Cryptoblade9623/zmk-config/Kicad Files/case left1.png

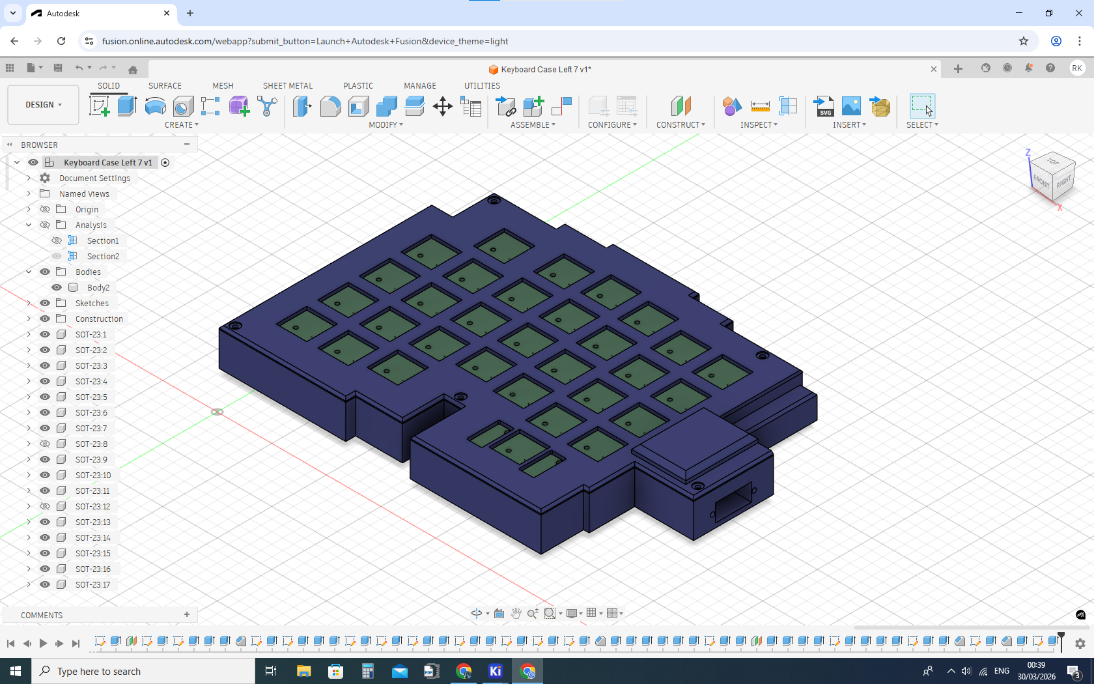
Kicad Files/case left1.png
