Cryptoblade9623/zmk-config/Kicad Files/case right1.png

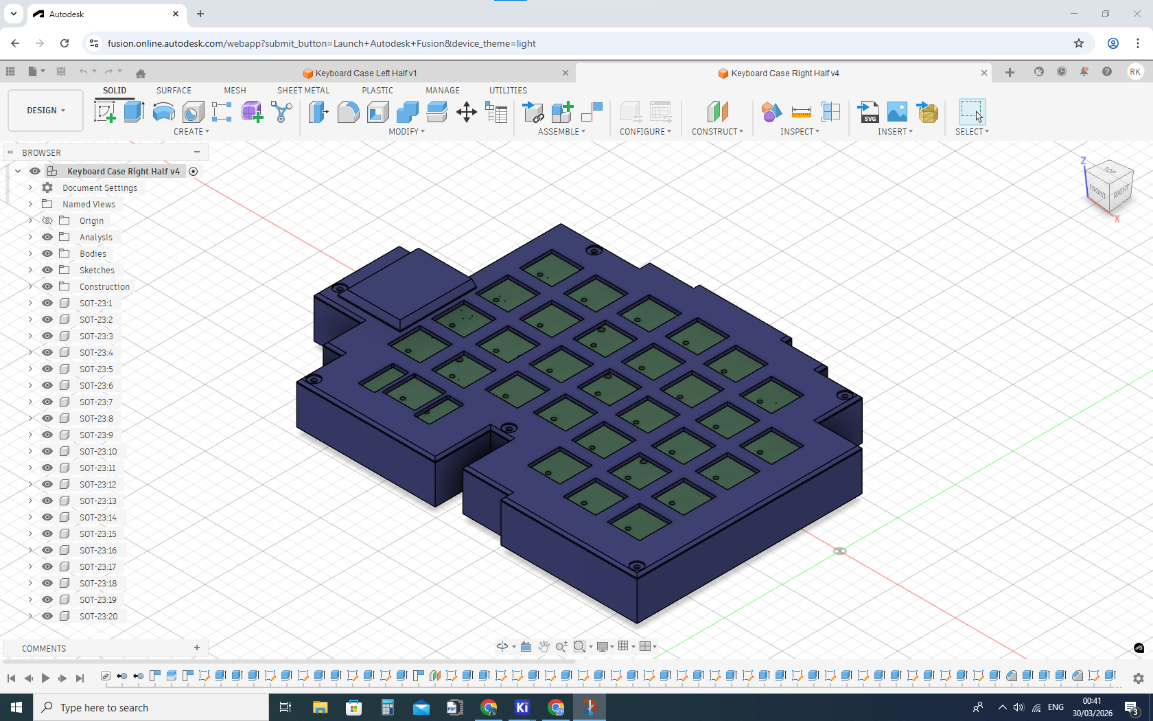
Kicad Files/case right1.png
